HerrRiebmann/Caravan_Leveler_2/Caravan_Leveler_2/data/Back.png

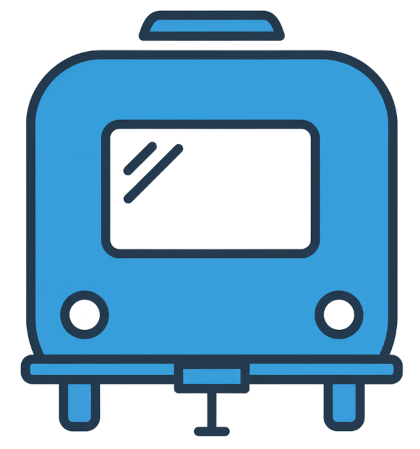
Caravan_Leveler_2/data/Back.png
