HerrRiebmann/Caravan_Leveler_2/Caravan_Leveler_2/data/Side.png

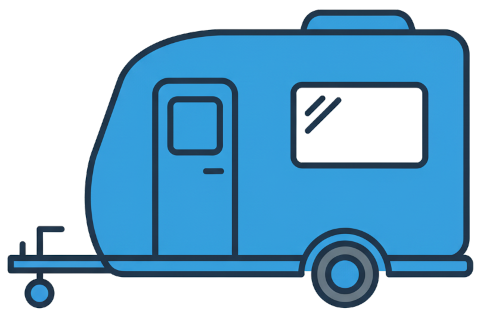
Caravan_Leveler_2/data/Side.png
