HerrRiebmann/Caravan_Leveler_2/Caravan_Leveler_2/Helper.ino

void SerialBegin() {
  Serial.begin(115200);
  logPrint("Start Leveler ");
  logPrintLn(ArduinoDateToDisplayDate(__DATE__));
}

void MPU6050Begin() {
  //accelInitialized = mpu.begin();
  Wire.begin(MPU_SDA, MPU_SCL);
  accelInitialized = mpu.begin(MPU_Adress, &Wire, 0);
  if (!accelInitialized) {
    logPrintLn("No MPU6050 detected ... Check your wiring!");
    TestI2C();
    return;
  }

  mpu.setAccelerometerRange(MPU6050_RANGE_8_G);
  mpu.setGyroRange(MPU6050_RANGE_500_DEG);
  mpu.setFilterBandwidth(MPU6050_BAND_21_HZ);
  
  logPrint("Accelerometer range set to: ");
  switch (mpu.getAccelerometerRange()) {
    case MPU6050_RANGE_2_G:
      logPrintLn("+-2G");
      break;
    case MPU6050_RANGE_4_G:
      logPrintLn("+-4G");
      break;
    case MPU6050_RANGE_8_G:
      logPrintLn("+-8G");
      break;
    case MPU6050_RANGE_16_G:
      logPrintLn("+-16G");
      break;
  }

  logPrint("Gyro range set to: ");
  switch (mpu.getGyroRange()) {
    case MPU6050_RANGE_250_DEG:
      logPrintLn("+- 250 deg/s");
      break;
    case MPU6050_RANGE_500_DEG:
      logPrintLn("+- 500 deg/s");
      break;
    case MPU6050_RANGE_1000_DEG:
      logPrintLn("+- 1000 deg/s");
      break;
    case MPU6050_RANGE_2000_DEG:
      logPrintLn("+- 2000 deg/s");
      break;
  }

  logPrint("Filter bandwidth set to: ");
  switch (mpu.getFilterBandwidth()) {
    case MPU6050_BAND_260_HZ:
      logPrintLn("260 Hz");
      break;
    case MPU6050_BAND_184_HZ:
      logPrintLn("184 Hz");
      break;
    case MPU6050_BAND_94_HZ:
      logPrintLn("94 Hz");
      break;
    case MPU6050_BAND_44_HZ:
      logPrintLn("44 Hz");
      break;
    case MPU6050_BAND_21_HZ:
      logPrintLn("21 Hz");
      break;
    case MPU6050_BAND_10_HZ:
      logPrintLn("10 Hz");
      break;
    case MPU6050_BAND_5_HZ:
      logPrintLn("5 Hz");
      break;
  }
}

void TestI2C() {
  Wire.begin(MPU_SDA, MPU_SCL);

  byte error, address;
  int nDevices;
  logPrintLn("Scanning...");
  nDevices = 0;
  for(address = 1; address < 127; address++ ) {
    Wire.beginTransmission(address);
    error = Wire.endTransmission();
    if (error == 0) {
      logPrint("I2C device found at address 0x");
      if (address<16) {
        logPrint("0");
      }
      logPrintLn(String(address,HEX));
      logPrintLn("Int: " + String(address));
      ReadWhoAmI(address);
      nDevices++;
    }
    else if (error==4) {
      logPrint("Unknow error at address 0x");
      if (address<16) {
        logPrint("0");
      }
      logPrintLn(String(address,HEX));
    }    
  }
  if (nDevices == 0) {
    logPrintLn("No I2C devices found\n");
  }
  else {
    logPrintLn("done\n");
  }
  Wire.end();
}

void ReadWhoAmI(byte address) {  
  Wire.beginTransmission(address);
  //Register: Who_Am_I
  Wire.write(0x75);
  Wire.endTransmission(false);
  Wire.requestFrom(address, (uint8_t)1);
  if (Wire.available()) {
    uint8_t whoAmI = Wire.read();
    logPrint("WHO_AM_I (0x75) = 0x");
    logPrintLn(String(whoAmI, HEX));
  } else {
    logPrintLn("WHO_AM_I: no response");
  }
}

void SpiffsBegin() {
#if USE_LITTLE_FS
  logPrint("LittleFS");
#else
  logPrint("SPIFFS");
#endif
  logPrint(" Update Target: ");
  logPrintLn(String(FS_PartitionStart));

  if (!SPIFFS.begin(true))
    logPrintLn("An Error has occurred while mounting the filesystem");
}

boolean isIp(String str) {
  logPrint("-IsIP: ");
  for (size_t i = 0; i < str.length(); i++) {
    int c = str.charAt(i);
    if (c != '.' && (c < '0' || c > '9')) {
      logPrintLn("false");
      return false;
    }
  }
  logPrintLn("true");
  return true;
}

bool ProcessETag(const char* ETag) {
  for (int i = 0; i < webServer.headers(); i++) {
    if (webServer.headerName(i).compareTo(F("If-None-Match")) == 0)
      if (webServer.header(i).compareTo(ETag) == 0) {
        webServer.send(304, "text/plain", F("Not Modified"));        
        logPrintLn(String(F("\t")) + webServer.headerName(i) + F(": ") + webServer.header(i));
        return true;
      }
  }
  webServer.sendHeader("ETag", ETag);
  webServer.sendHeader("Cache-Control", "public");
  return false;
}

void ProcessSetupArguments() {
  // /setup?x=123&y=321&inv=0&ap=1&t=10

  bool voltageChanged = false;
  bool mpu6050Changed = false;

  for (uint8_t i = 0; i < webServer.args(); i++) {    
    logPrintLn(String(F(" ")) + webServer.argName(i) + F(": ") + webServer.arg(i));

    if (webServer.argName(i).compareTo(F("inv")) == 0) {
      invertAxis = webServer.arg(i).toInt();
      StoreInvertation();
    }

    if (webServer.argName(i).compareTo(F("ap")) == 0) {
      useAcessPointMode = webServer.arg(i) == "1";
      StoreAP();
    }
    if (webServer.argName(i).compareTo(F("apw")) == 0) {
      devicePassword = webServer.arg(i);
      StoreAP();
    }

    if (webServer.argName(i).compareTo(F("t")) == 0) {
      int j = webServer.arg(i).toInt();
      if (j > 0 && j <= 90) {
        levelThreshold = j;
        StoreLevelThreshold();
      }
    }

    if (webServer.argName(i).compareTo(F("s")) == 0) {
      Serial_Enabled = webServer.arg(i) == "1";
      StoreSerial();
    }
    if (webServer.argName(i).compareTo(F("dmp")) == 0) {
      dampingEnabled = webServer.arg(i) == "1";
      StoreDamping();
    }
    if (webServer.argName(i).compareTo(F("v")) == 0) {
      voltThreshold = webServer.arg(i).toInt() / 100.0;
      voltageChanged = true;
    }
    if (webServer.argName(i).compareTo(F("vp")) == 0) {
      voltagePin = webServer.arg(i).toInt();
      voltageChanged = true;
    }
    if (webServer.argName(i).compareTo(F("r1")) == 0) {
      resistor1 = webServer.arg(i).toFloat();
      voltageChanged = true;
    }
    if (webServer.argName(i).compareTo(F("r2")) == 0) {
      resistor2 = webServer.arg(i).toFloat();
      voltageChanged = true;
    }

    if (webServer.argName(i).compareTo(F("sda")) == 0) {
      MPU_SDA = webServer.arg(i).toInt();
      mpu6050Changed = true;
    }
    if (webServer.argName(i).compareTo(F("scl")) == 0) {
      MPU_SCL = webServer.arg(i).toInt();
      mpu6050Changed = true;
    }
    if (webServer.argName(i).compareTo(F("add")) == 0) {
      MPU_Adress = webServer.arg(i).toInt();
      mpu6050Changed = true;
    }
  }

  if (voltageChanged)
    StoreVoltageSettings();
  if(mpu6050Changed) {
    StoreI2CSetup();
    Wire.end();
    MPU6050Begin();
  }
}

String toStringIp(IPAddress ip) {  
  logPrintLn("IptoString");
  String res = "";
  for (int i = 0; i < 3; i++) {
    res += String((ip >> (8 * i)) & 0xFF) + ".";
  }
  res += String(((ip >> 8 * 3)) & 0xFF);
  return res;
}

String GetEncryptionType(byte thisType) {
  // read the encryption type and print out the name:
  switch (thisType) {
    case 0:
      return "OPEN";
    case 1:
      return "WEP";
    case 2:
      return "WPA_PSK";
    case 3:
      return "WPA2_PSK";
    case 4:
      return "WPA_WPA2_PSK";
    case 5:
      return "WPA2_ENTERPRISE";
    case 6:
      return "AUTH_MAX";
  }
  return "Unknown: " + String(thisType);
}
String runtime(uint32_t currentMillis) {
  uint32_t sec{ (currentMillis / 1000) };
  char buf[20];
  if (sec / 86400 > 1)
    snprintf(buf, sizeof(buf), "%d Tag%s %02d:%02d:%02d", sec / 86400, sec < 86400 || sec >= 172800 ? "e" : "", sec / 3600 % 24, sec / 60 % 60, sec % 60);
  else
    snprintf(buf, sizeof(buf), "%02d:%02d:%02d", sec / 3600 % 24, sec / 60 % 60, sec % 60);
  return buf;
}
const String formatBytes(size_t const& bytes) {
  return " (" + (bytes < 1024 ? static_cast<String>(bytes) + " Byte" : bytes < 1048576 ? static_cast<String>(bytes / 1024.0) + " KB"
                                                                                       : static_cast<String>(bytes / 1048576.0) + " MB")
         + ")";
}
// Adapted from http://stackoverflow.com/questions/1765014/convert-string-from-date-into-a-time-t
// Formats __DATE__ to YYYY.MM.DD format
String ArduinoDateToDisplayDate(char const *time) { 
    char s_month[5];
    int month, day, year;
    static const char month_names[] = "JanFebMarAprMayJunJulAugSepOctNovDec";

    sscanf(time, "%s %d %d", s_month, &day, &year);

    month = (strstr(month_names, s_month)-month_names)/3;
    //Starting at 0
    month += 1;

    String monthText = month < 10 ? "0" + String(month) : String(month);
    String dayText = day < 10 ? "0" + String(day) : String(day);

    return String(year) + "." + monthText + "." + dayText;
}
void ResetWebTimer() {
  lastMillisClientAvailable = millis();
  voltage_read = false;
}
void logPrintLn(const String& msg) {
  logPrint(msg, true);
}

void logPrint(const String& msg, bool linebreak) {
  if(!Serial_Enabled)
    return;
  logBuffer.concat(msg);
  if (linebreak) {
    Serial.println(msg);
    logBuffer.concat("\n");
  } else {
    Serial.print(msg);
  }
  if (logBuffer.length() > 10000) {
    logBuffer.remove(0, 1000);
  }
}
