HerrRiebmann/Caravan_Leveler_2/Caravan_Leveler_2/Data.ino

void LoadData() {
  //Readonly: false
  settings.begin("settings", false);
  //Variable Name: Max 15 chars!!!!

  LoadLevel();
  LoadLevelThreshold();
  LoadInvertation();
  LoadAP();
  LoadWiFi();
  LoadSerial();
  LoadDamping();
  LoadVoltageSettings();
  LoadI2CSetup();

  settings.end();
}
void LoadLevel() {
  calibrationX = settings.getFloat("calibrationX", calibrationX);
  calibrationY = settings.getFloat("calibrationY", calibrationY);

  logPrint("Loaded Calibration X: ");
  logPrint(String(calibrationX));
  logPrint(" Y: ");
  logPrintLn(String(calibrationY));
}

void LoadLevelThreshold() {
  levelThreshold = settings.getInt("levelThreshold", levelThreshold);

  logPrint("Loaded Threshold: ");
  logPrintLn(String(levelThreshold));
}
void LoadInvertation() {
  invertAxis = settings.getInt("invertAxis", invertAxis);

  logPrint(String(F("Loaded Inverted Axis: ")));
  logPrintLn(String(invertAxis));
}

void LoadAP() {
  useAcessPointMode = settings.getBool("useAPMode", useAcessPointMode);
  devicePassword = settings.getString("devicePassword", devicePassword);
  logPrint(String(F("Loaded AccessPoint: ")));
  logPrintLn(useAcessPointMode ? "True" : "False");
}
void LoadWiFi(){
  ssid = settings.getString("ssid", ssid);
  password = settings.getString("password", password);
  logPrint(String(F("Loaded SSID: ")));
  logPrintLn(ssid);
}
void LoadSerial() {
  Serial_Enabled = settings.getBool("serialEnabled", Serial_Enabled);
  
  logPrint(String(F("Serial Output enabled: ")));
  logPrintLn(Serial_Enabled ? "True": "False");
}
void LoadDamping() {
  dampingEnabled = settings.getBool("damping", dampingEnabled);

  logPrint(String(F("Damping enabled: ")));
  logPrintLn(dampingEnabled ? "True" : "False");
}
void LoadVoltageSettings() {
  voltThreshold = settings.getFloat("voltThreshold", voltThreshold);
  voltagePin = settings.getInt("voltagePin", voltagePin);
  resistor1 = settings.getInt("resistor1", resistor1);
  resistor2 = settings.getInt("resistor2", resistor2);
  
  logPrint(String(F("Loaded Voltage Threshold: ")));
  logPrintLn(String(voltThreshold));
  logPrint(String(F("Pin: ")));
  logPrintLn(String(voltagePin));
  logPrint(String(F("R1: ")));
  logPrintLn(String(resistor1));
  logPrint(String(F("R2: ")));
  logPrintLn(String(resistor2));
}

void LoadI2CSetup() {
  MPU_SDA = settings.getInt("MPU_SDA", SDA);
  MPU_SCL = settings.getInt("MPU_SCL", SCL);
  MPU_Adress = settings.getInt("MPU_Adress", 0x68);

  logPrint("SDA: ");
  logPrint(String(MPU_SDA));
  logPrint(" SCL: ");
  logPrint(String(MPU_SCL));
  logPrint(" Adress: ");
  logPrintLn(String(MPU_Adress, HEX));
}

void StoreLevel() {
  settings.begin("settings", false);
  settings.putFloat("calibrationX", calibrationX);
  settings.putFloat("calibrationY", calibrationY);
  settings.end();
}
void StoreLevelThreshold() {
  settings.begin("settings", false);
  settings.putInt("levelThreshold", levelThreshold);
  settings.end();
}
void StoreInvertation() {
  settings.begin("settings", false);
  settings.putInt("invertAxis", invertAxis);
  settings.end();
}

void StoreAP() {
  settings.begin("settings", false);
  settings.putBool("useAPMode", useAcessPointMode);
  settings.putString("devicePassword", devicePassword);
  settings.end();
}
void StoreWiFi(){
  settings.begin("settings", false);
  settings.putString("ssid", ssid);
  settings.putString("password", password);
  settings.end();
}
void StoreSerial() {
  settings.begin("settings", false);
  settings.putBool("serialEnabled", Serial_Enabled);
  settings.end();
}
void StoreDamping() {
  settings.begin("settings", false);
  settings.putBool("damping", dampingEnabled);
  settings.end();
}
void StoreVoltageSettings() {
  settings.begin("settings", false);
  settings.putFloat("voltThreshold", voltThreshold);
  settings.putInt("voltagePin", voltagePin);
  settings.putInt("resistor1", resistor1);
  settings.putInt("resistor2", resistor2);
  settings.end();
}
void StoreI2CSetup() {
  settings.begin("settings", false);
  settings.putInt("MPU_SDA", MPU_SDA);
  settings.putInt("MPU_SCL", MPU_SCL);
  settings.putInt("MPU_Adress", MPU_Adress);
  settings.end();
}
